dd-jero/3-axis-Gimbal-that-tracks-light/STL File/flat_su.stl

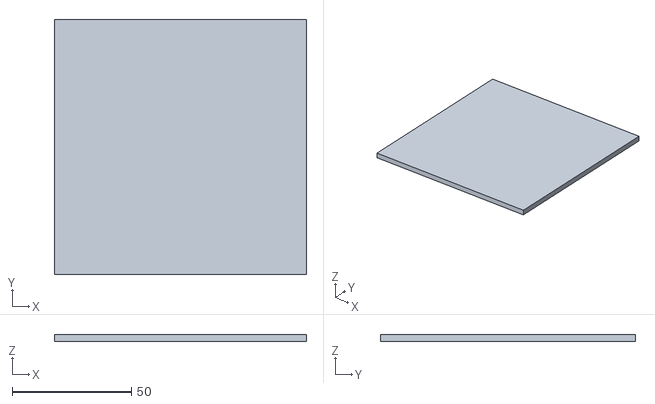
[picture p40: CAD file, 2022-08-05]
STL File/flat_su.stl
105.6 x 106.8 x 3.04
